La-Wei/Prophet-VS/doc/prophet_vs_service_context/page_notes/5508/page_004.md

# 5508 pagina 4

Source: `doc/5508.pdf` pagina 4  
Immagine: [5508/page_004.png](../../page_images/5508/page_004.png)  
Testo/OCR: [5508/page_004.txt](../../extracted_text/5508/page_004.txt)  
Metodo testo: `ocr`, confidenza: `medium`

## Cosa sembra contenere questa pagina
PD508 input/output considerations. Tipo pagina: datasheet, sample & hold.

## Etichette / componenti / IC / net visibili
- IC / chip: PD508
- Resistenze / capacitori / reti: [NON CHIARO]
- Connettori / test point: [NON CHIARO]
- Rail: -5V, VSS
- Net nominate: RIGHT

## Riassunto funzione del circuito
Confermato dalle etichette:
- Pagina con input/output considerations, sorgente a bassa impedenza/op amp e capacitori di feedback.

Inferenza ragionevole:
- Utile per leakage, caricamento uscita e stabilita dei CV.

Incerto / da verificare manualmente:
- OCR e scansione non garantiscono valori completi; verificare sempre l'immagine pagina.
- Non assumere che una modifica ECR sia presente sulla macchina reale senza ispezione fisica.

## Rilevanza per riparazione
- Utile per collegare sintomi a pagine sorgente e localizzare componenti o net sul Prophet VS.
- Se la pagina contiene artwork/layout, usarla per ispezione fisica: piste, jumper, tagli, saldature, riparazioni precedenti.
- Se la pagina contiene schema, usarla per ragionare su rail, segnali, connettori e possibili cause, senza trattare l'OCR come prova definitiva.

## Possibili failure mode collegati a questa pagina
- Saldatura crepata, pista/via danneggiata, connettore ossidato o riparazione precedente non conforme.
- Componente attivo guasto o alimentazione fuori specifica nei blocchi mostrati.
- Condensatore in perdita, valore resistenza errato o rete resistiva modificata male, se applicabile alla pagina.
- CV bleed/droop, op amp guasto, analog switch/S&H guasto, ground analogico/digitale contaminato o ripple sui rail quando la pagina mostra circuiti analogici/CV.

## Cross-reference
- [5508 pagina 3](page_003.md)
- [5530 pagina 4](../5530/page_004.md)
