La-Wei/Prophet-VS/doc/prophet_vs_service_context/page_notes/5530/page_002.md

# 5530 pagina 2

Source: `doc/5530.pdf` pagina 2  
Immagine: [5530/page_002.png](../../page_images/5530/page_002.png)  
Testo/OCR: [5530/page_002.txt](../../extracted_text/5530/page_002.txt)  
Metodo testo: `ocr`, confidenza: `low`

## Cosa sembra contenere questa pagina
CEM5530 pinout/diagram, OCR scarso. Tipo pagina: datasheet, sample & hold, pinout.

## Etichette / componenti / IC / net visibili
- IC / chip: CEM5530
- Resistenze / capacitori / reti: [NON CHIARO]
- Connettori / test point: [NON CHIARO]
- Rail: [NON CHIARO]
- Net nominate: [NON CHIARO]

## Riassunto funzione del circuito
Confermato dalle etichette:
- OCR scarso; sembra diagramma/pinout del CEM5530.

Inferenza ragionevole:
- Usare l'immagine per pinout se serve, non affidarsi solo all'OCR.

Incerto / da verificare manualmente:
- OCR e scansione non garantiscono valori completi; verificare sempre l'immagine pagina.
- Non assumere che una modifica ECR sia presente sulla macchina reale senza ispezione fisica.

## Rilevanza per riparazione
- Utile per collegare sintomi a pagine sorgente e localizzare componenti o net sul Prophet VS.
- Se la pagina contiene artwork/layout, usarla per ispezione fisica: piste, jumper, tagli, saldature, riparazioni precedenti.
- Se la pagina contiene schema, usarla per ragionare su rail, segnali, connettori e possibili cause, senza trattare l'OCR come prova definitiva.

## Possibili failure mode collegati a questa pagina
- Saldatura crepata, pista/via danneggiata, connettore ossidato o riparazione precedente non conforme.
- Componente attivo guasto o alimentazione fuori specifica nei blocchi mostrati.
- Condensatore in perdita, valore resistenza errato o rete resistiva modificata male, se applicabile alla pagina.
- CV bleed/droop, op amp guasto, analog switch/S&H guasto, ground analogico/digitale contaminato o ripple sui rail quando la pagina mostra circuiti analogici/CV.

## Cross-reference
- [5530 pagina 1](page_001.md)
- [5530 pagina 3](page_003.md)
