La-Wei/Prophet-VS/doc/prophet_vs_service_context/page_notes/sci_prophet_vs_ecr738/page_003.md

# sci_prophet_vs_ecr738 pagina 3

Source: `doc/sci_prophet_vs_ecr738.pdf` pagina 3  
Immagine: [sci_prophet_vs_ecr738/page_003.png](../../page_images/sci_prophet_vs_ecr738/page_003.png)  
Testo/OCR: [sci_prophet_vs_ecr738/page_003.txt](../../extracted_text/sci_prophet_vs_ecr738/page_003.txt)  
Metodo testo: `ocr`, confidenza: `low`

## Cosa sembra contenere questa pagina
ECR 738, dettaglio board/artwork poco leggibile. Tipo pagina: board artwork / layout, ECR / engineering change record.

## Etichette / componenti / IC / net visibili
- IC / chip: [NON CHIARO]
- Resistenze / capacitori / reti: [NON CHIARO]
- Connettori / test point: [NON CHIARO]
- Rail: [NON CHIARO]
- Net nominate: [NON CHIARO]

## Riassunto funzione del circuito
Confermato dalle etichette:
- OCR molto scarso; si legge solo parzialmente OSCIL/BOARD e testo non affidabile.

Inferenza ragionevole:
- Probabile immagine di riferimento fisico/artwork collegata alla modifica ECR 738.

Incerto / da verificare manualmente:
- OCR e scansione non garantiscono valori completi; verificare sempre l'immagine pagina.
- Non assumere che una modifica ECR sia presente sulla macchina reale senza ispezione fisica.

## Rilevanza per riparazione
- Utile per collegare sintomi a pagine sorgente e localizzare componenti o net sul Prophet VS.
- Se la pagina contiene artwork/layout, usarla per ispezione fisica: piste, jumper, tagli, saldature, riparazioni precedenti.
- Se la pagina contiene schema, usarla per ragionare su rail, segnali, connettori e possibili cause, senza trattare l'OCR come prova definitiva.

## Possibili failure mode collegati a questa pagina
- Saldatura crepata, pista/via danneggiata, connettore ossidato o riparazione precedente non conforme.
- Componente attivo guasto o alimentazione fuori specifica nei blocchi mostrati.
- Condensatore in perdita, valore resistenza errato o rete resistiva modificata male, se applicabile alla pagina.
- CV bleed/droop, op amp guasto, analog switch/S&H guasto, ground analogico/digitale contaminato o ripple sui rail quando la pagina mostra circuiti analogici/CV.

## Cross-reference
- [sci_prophet_vs_ecr738 pagina 2](page_002.md)
