La-Wei/Prophet-VS/doc/prophet_vs_service_context/page_notes/sci_prophet_vs_ecr739/page_003.md

# sci_prophet_vs_ecr739 pagina 3

Source: `doc/sci_prophet_vs_ecr739.pdf` pagina 3  
Immagine: [sci_prophet_vs_ecr739/page_003.png](../../page_images/sci_prophet_vs_ecr739/page_003.png)  
Testo/OCR: [sci_prophet_vs_ecr739/page_003.txt](../../extracted_text/sci_prophet_vs_ecr739/page_003.txt)  
Metodo testo: `ocr`, confidenza: `unavailable`

## Cosa sembra contenere questa pagina
ECR 739, pagina quasi illeggibile. Tipo pagina: ECR / engineering change record, board revision.

## Etichette / componenti / IC / net visibili
- IC / chip: [NON CHIARO]
- Resistenze / capacitori / reti: [NON CHIARO]
- Connettori / test point: [NON CHIARO]
- Rail: [NON CHIARO]
- Net nominate: [NON CHIARO]

## Riassunto funzione del circuito
Confermato dalle etichette:
- OCR quasi nullo; non usare questa pagina senza ispezione immagine manuale.

Inferenza ragionevole:
- Possibile pagina intermedia o allegato della modifica ECR 739.

Incerto / da verificare manualmente:
- OCR e scansione non garantiscono valori completi; verificare sempre l'immagine pagina.
- Non assumere che una modifica ECR sia presente sulla macchina reale senza ispezione fisica.

## Rilevanza per riparazione
- Utile per collegare sintomi a pagine sorgente e localizzare componenti o net sul Prophet VS.
- Se la pagina contiene artwork/layout, usarla per ispezione fisica: piste, jumper, tagli, saldature, riparazioni precedenti.
- Se la pagina contiene schema, usarla per ragionare su rail, segnali, connettori e possibili cause, senza trattare l'OCR come prova definitiva.

## Possibili failure mode collegati a questa pagina
- Saldatura crepata, pista/via danneggiata, connettore ossidato o riparazione precedente non conforme.
- Componente attivo guasto o alimentazione fuori specifica nei blocchi mostrati.
- Condensatore in perdita, valore resistenza errato o rete resistiva modificata male, se applicabile alla pagina.
- CV bleed/droop, op amp guasto, analog switch/S&H guasto, ground analogico/digitale contaminato o ripple sui rail quando la pagina mostra circuiti analogici/CV.

## Cross-reference
- [sci_prophet_vs_ecr739 pagina 4](page_004.md)
