La-Wei/Prophet-VS/doc/prophet_vs_service_context/diagnostic_notes/README.md

# Diagnostic notes

Queste note sono un albero di ipotesi, non una diagnosi certa. Ogni ipotesi rimanda alle pagine sorgente generate in questa knowledge base. Partire da `symptom_audio_at_volume_zero.md` se il problema principale e' bleed/distorsione a volume zero.
