La-Wei/Prophet-VS/tecnico/05_pagine_rilevanti/note/5530/page_002.md

# 5530 pagina 2

Source: `../../../06_pdf_originali/5530.pdf` pagina 2  
Immagine: [5530/page_002.png](../../immagini/5530/page_002.png)  

## Cosa sembra contenere questa pagina

Pinout/diagramma interno del `CEM5530`.

## Note utili per ricambi e dissipazione

- La pagina mostra un package con pin numerati da `1` a `40`.
- Nel Prophet VS i due `CEM5530` rilevanti sono `U449` e `U425`.
- Per dissipatori adesivi sul corpo del chip, comprare due dissipatori identici: uno per `U449` e uno per `U425`.

## Avvertenza

L'OCR di questa pagina e' scarso: usare l'immagine per confermare pinout e orientamento, non il testo estratto.

## Cross-reference

- [5530 pagina 1](page_001.md)
- [5530 pagina 3](page_003.md)
- [5530 pagina 4](page_004.md)
- [pvs_service pagina 6](../pvs_service/page_006.md)
