La-Wei/Prophet-VS/doc/prophet_vs_service_context/page_images/5508/page_003.png

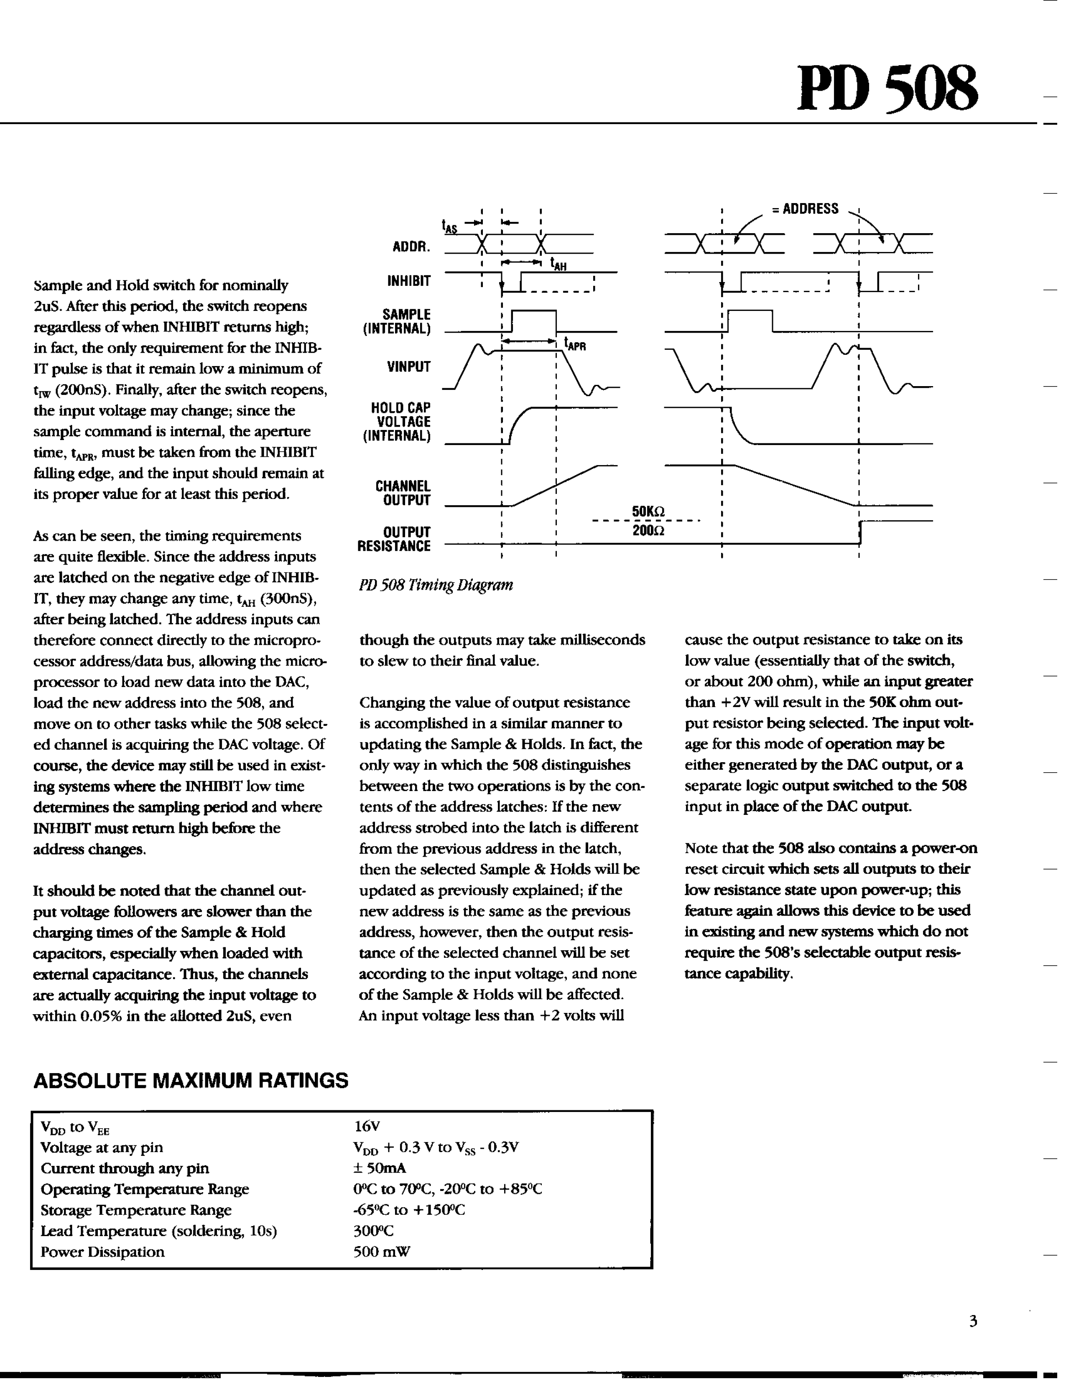
doc/prophet_vs_service_context/page_images/5508/page_003.png
