La-Wei/Prophet-VS/doc/prophet_vs_service_context/page_images/5530/page_004.png

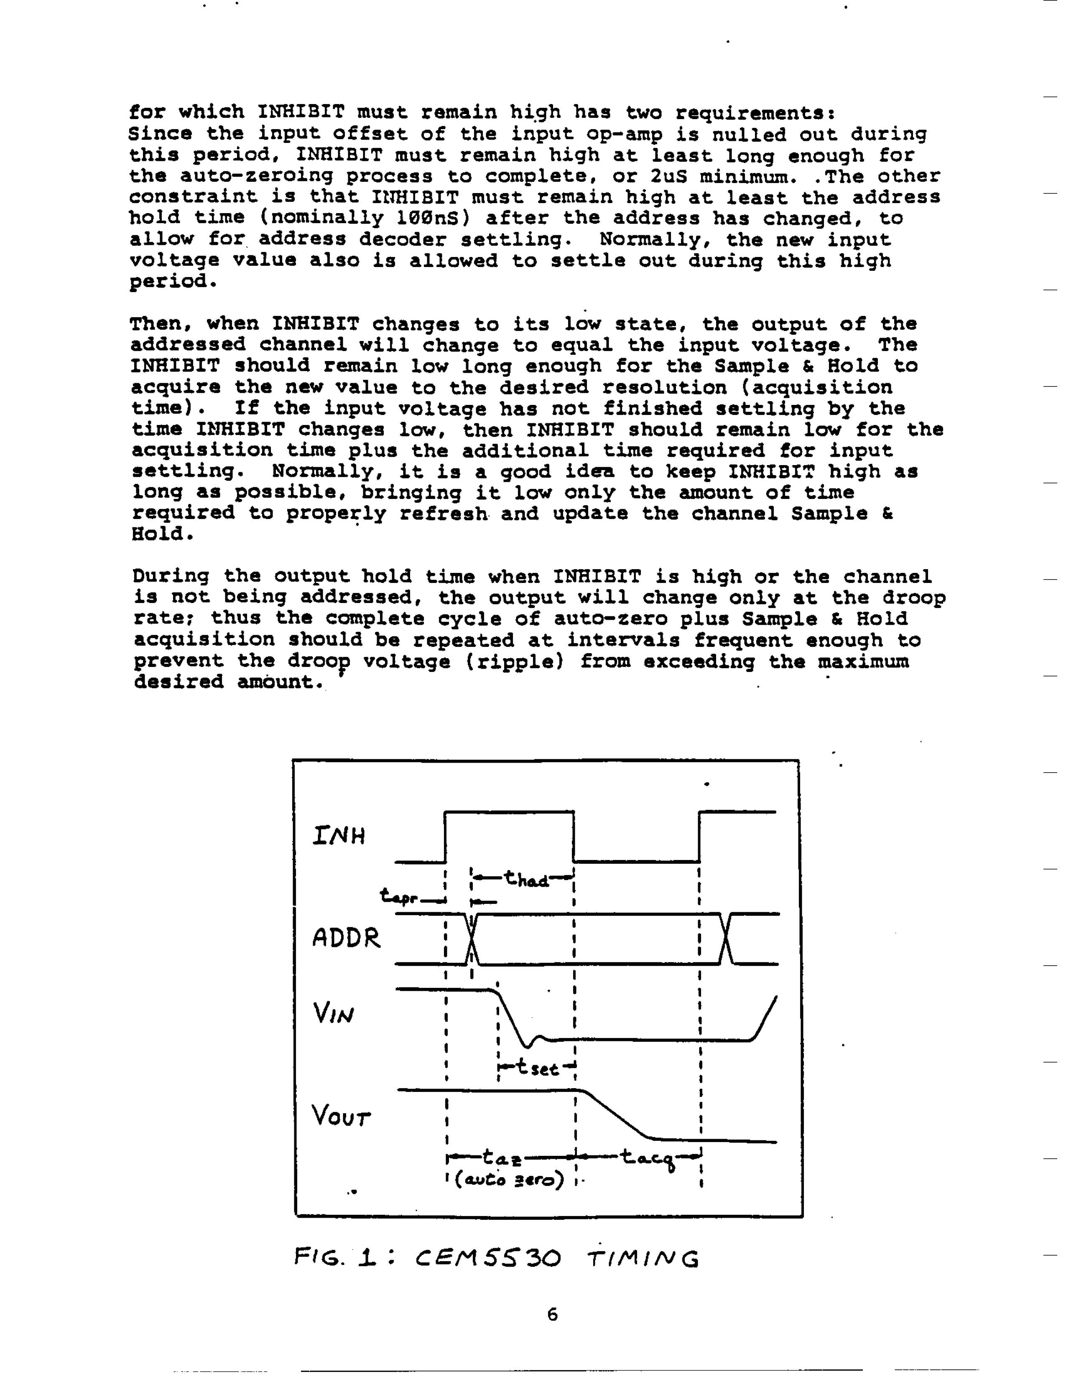
doc/prophet_vs_service_context/page_images/5530/page_004.png
