La-Wei/Prophet-VS/doc/prophet_vs_service_context/page_images/pvs_service/page_006.png

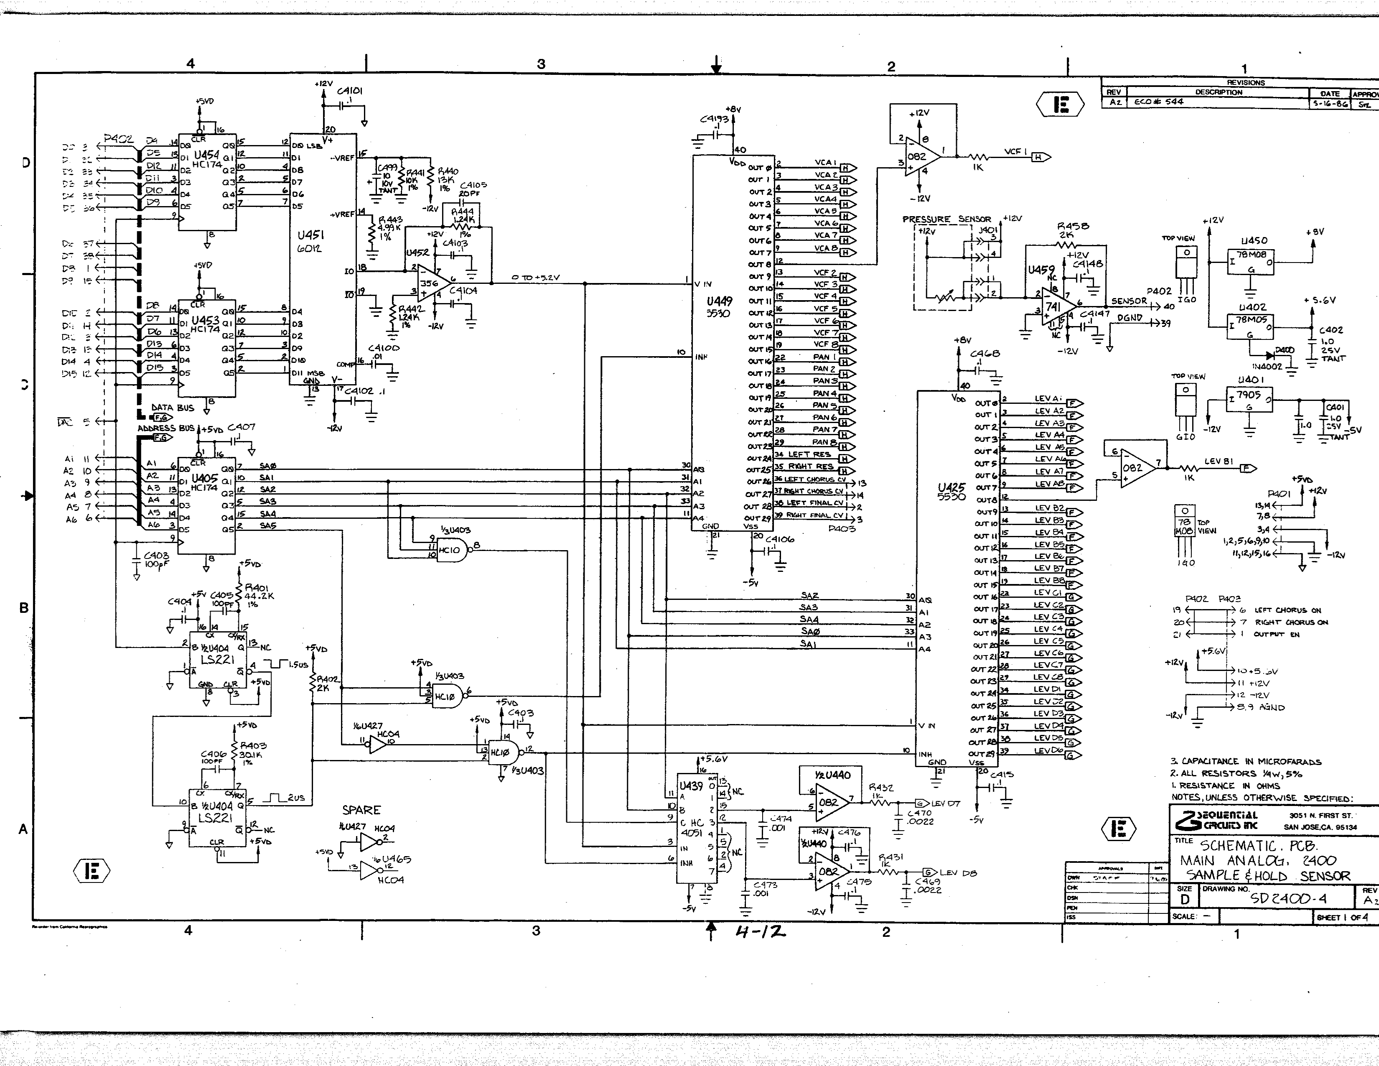
doc/prophet_vs_service_context/page_images/pvs_service/page_006.png
