La-Wei/Prophet-VS/doc/prophet_vs_service_context/page_images/pvs_service/page_010.png

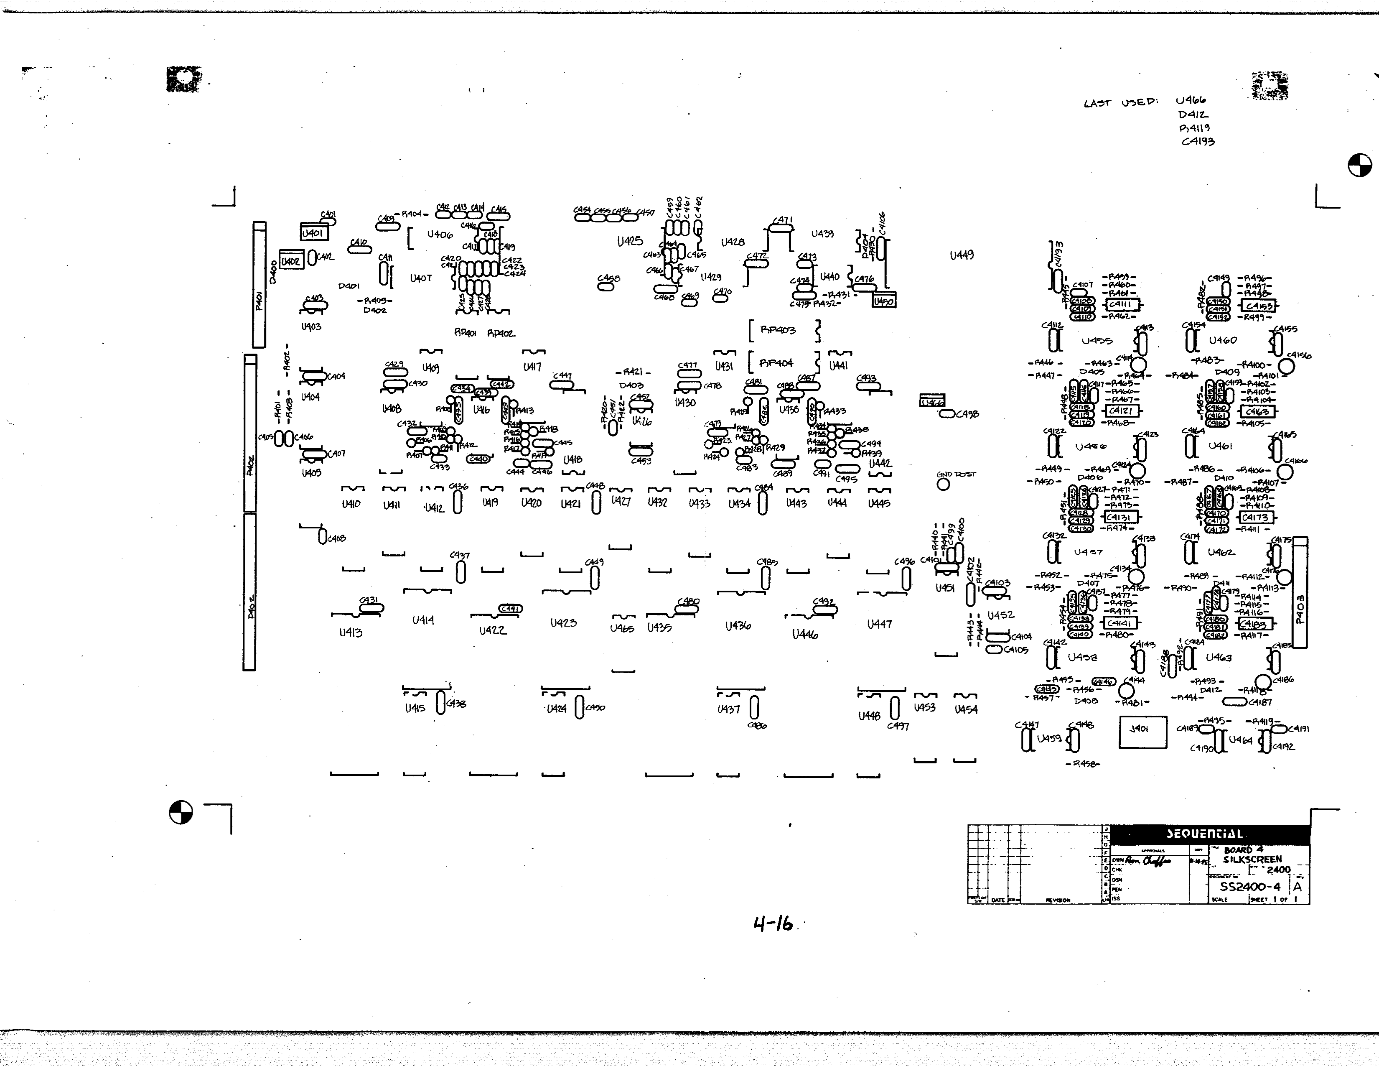
doc/prophet_vs_service_context/page_images/pvs_service/page_010.png
