La-Wei/Prophet-VS/doc/prophet_vs_service_context/page_images/pvs_service/page_012.png

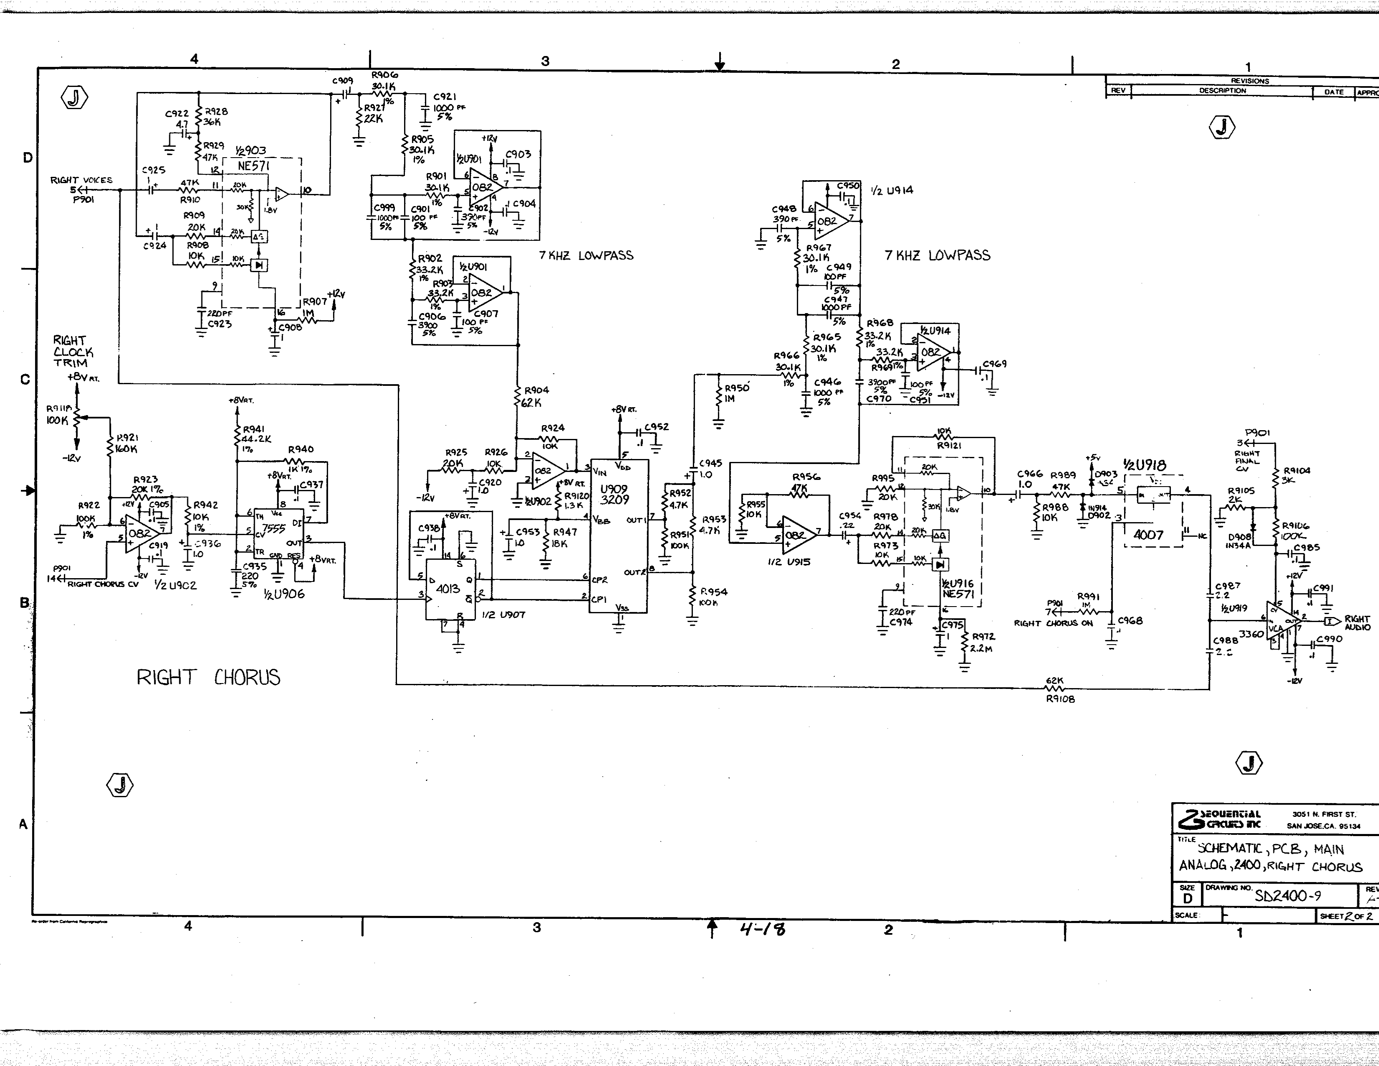
doc/prophet_vs_service_context/page_images/pvs_service/page_012.png
