La-Wei/Prophet-VS/doc/prophet_vs_service_context/page_images/sci_prophet_vs_ecr739/page_003.png

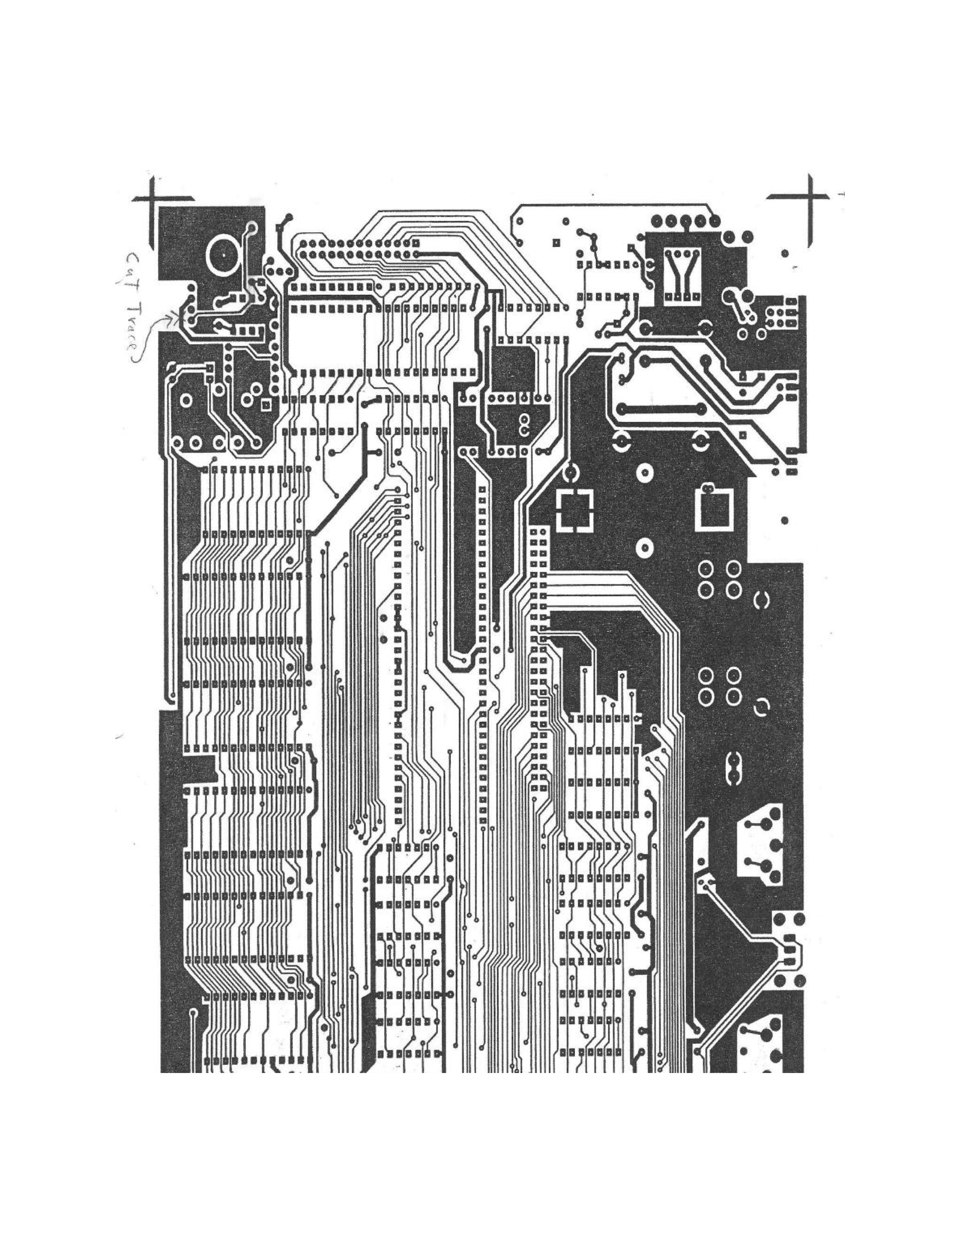
doc/prophet_vs_service_context/page_images/sci_prophet_vs_ecr739/page_003.png
