La-Wei/Prophet-VS/tecnico/05_pagine_rilevanti/immagini/5530/page_002.png

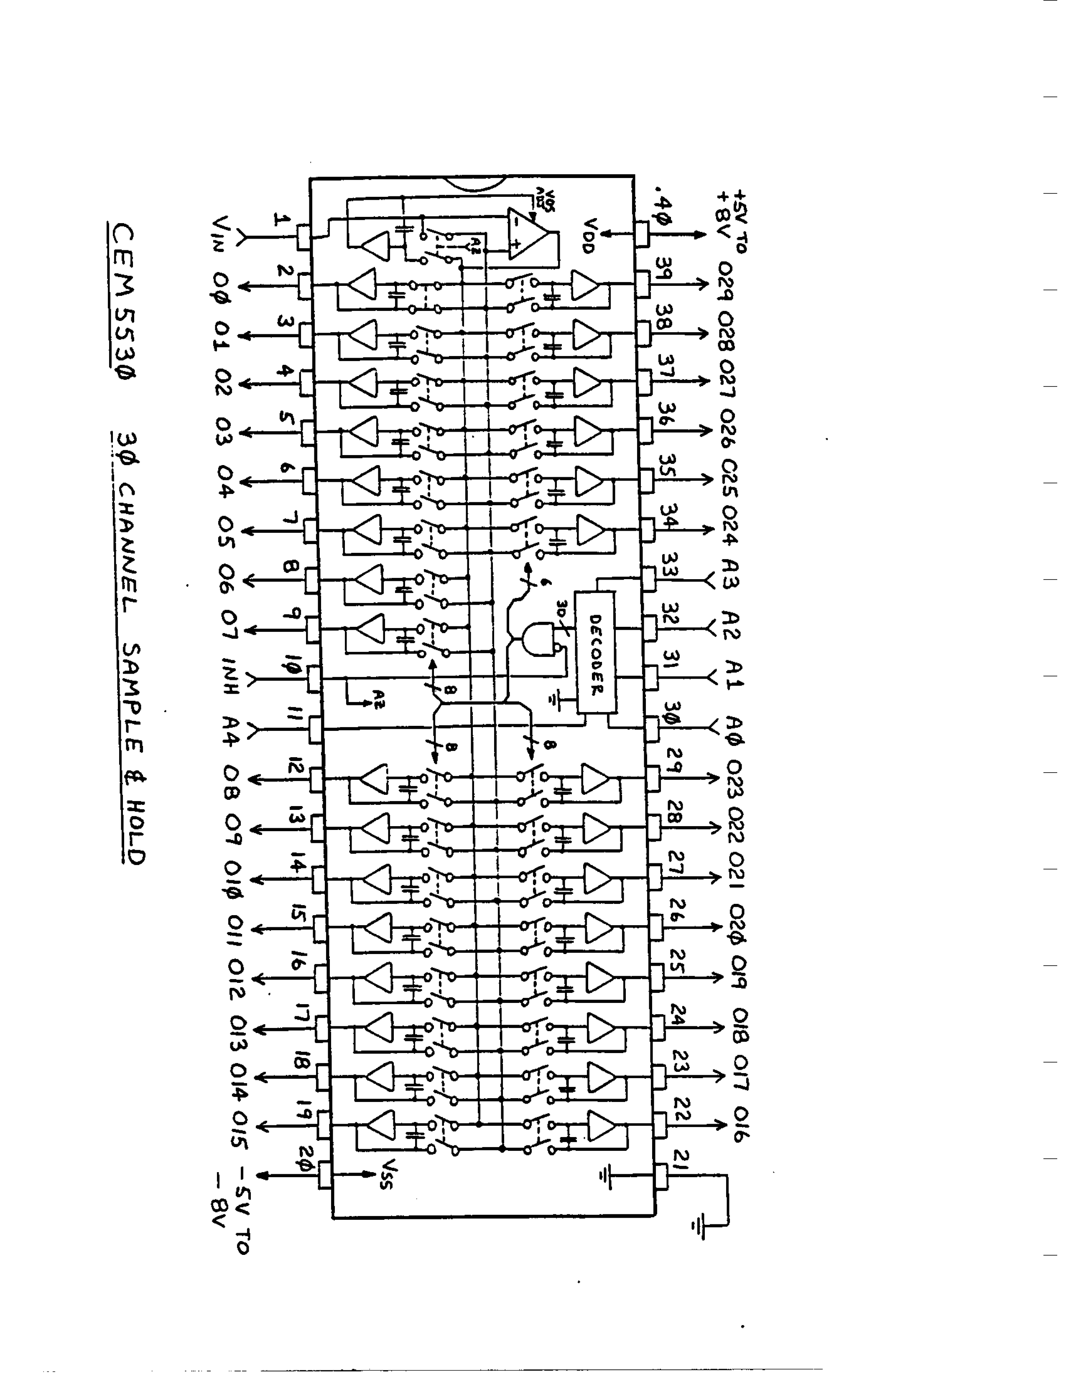
tecnico/05_pagine_rilevanti/immagini/5530/page_002.png
